nuprobotics/mqtt_traffic_light/documentation/pictures/20241231_001149.jpg

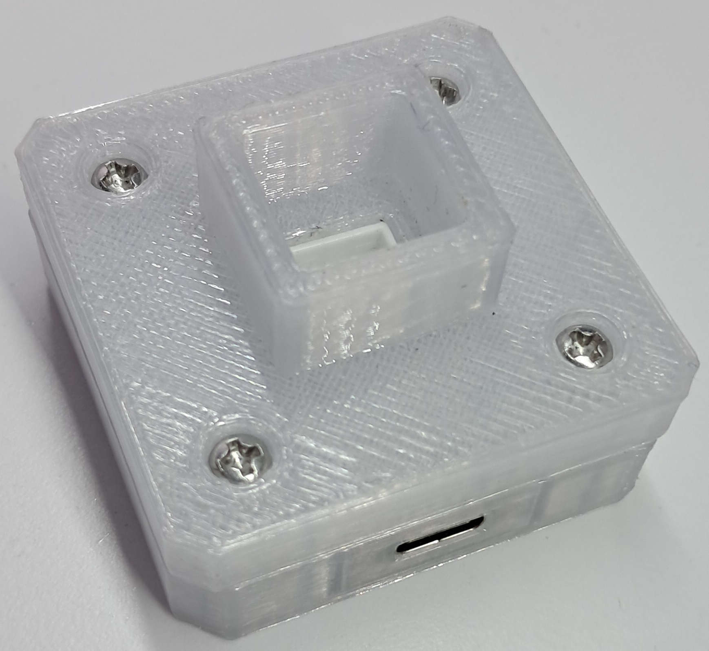
documentation/pictures/20241231_001149.jpg
