nuprobotics/mqtt_traffic_light/CAD_models/base.FCStd

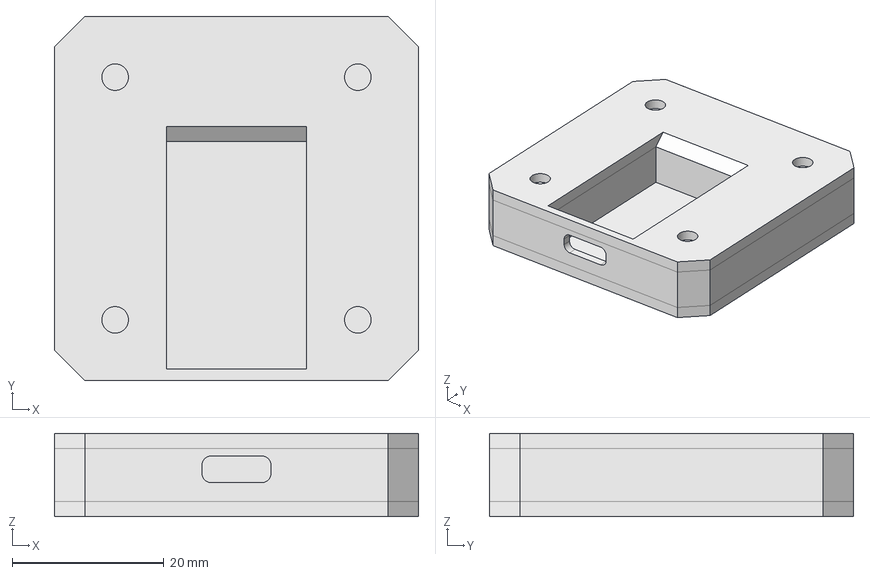
[picture p8: CAD file, 2024-12-30]
CAD_models/base.FCStd
48.0 x 48.0 x 11.0 mm
