nuprobotics/mqtt_traffic_light/CAD_models/base_lid.FCStd

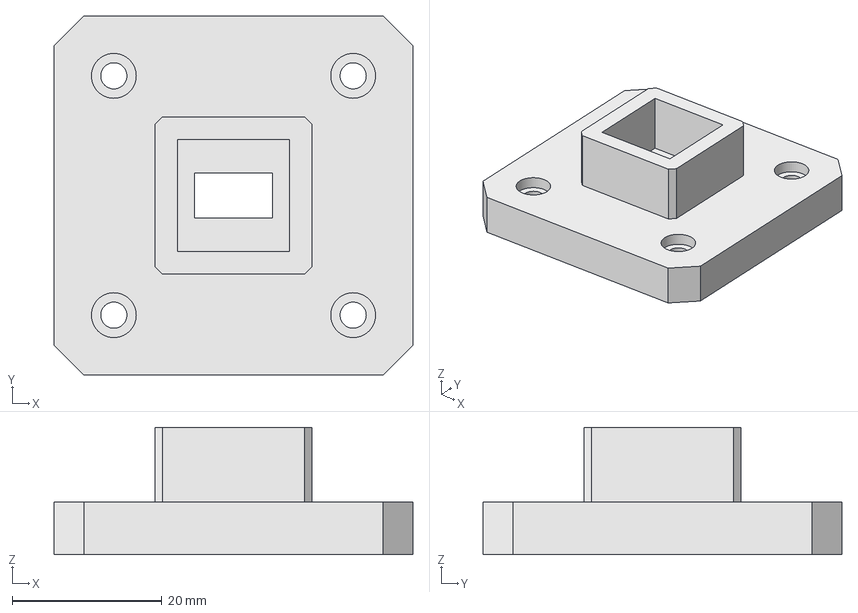
[picture p9: CAD file, 2024-12-30]
CAD_models/base_lid.FCStd
48.0 x 48.0 x 17.0 mm
